Mario170000/Proiect---OpenBook/Images/Battery_OpenBook.PNG

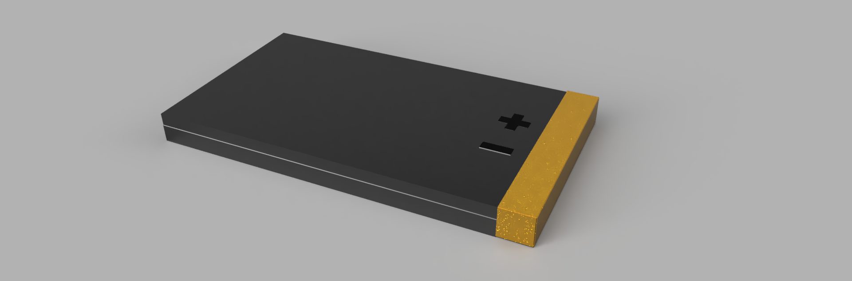
Images/Battery_OpenBook.PNG
